PaFDC/CTS-Maker-Kit/apps/CTS_Fabric_Gui/data/list.png

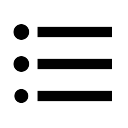
apps/CTS_Fabric_Gui/data/list.png
