PaFDC/CTS-Maker-Kit/apps/CTS_Fabric_Gui/data/pause.png

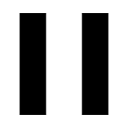
apps/CTS_Fabric_Gui/data/pause.png
