PaFDC/CTS-Maker-Kit/apps/CTS_Fabric_Gui/data/play.png

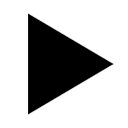
apps/CTS_Fabric_Gui/data/play.png
