PaFDC/CTS-Maker-Kit/apps/CTS_Fabric_Gui/data/reset.png

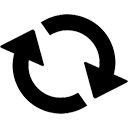
apps/CTS_Fabric_Gui/data/reset.png
